vicadel/3D-TFG-VICADEL/STLs/Rotation-Wrist/RotaWrist2V3.stl

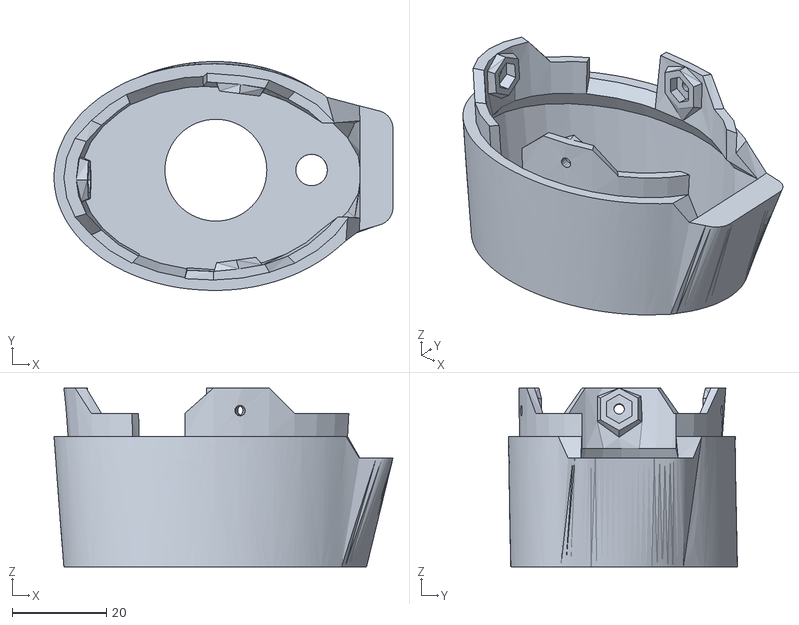
[picture p15: CAD file, 2024-09-07]
STLs/Rotation-Wrist/RotaWrist2V3.stl
71.9 x 48.6 x 38.0
