vicadel/3D-TFG-VICADEL/STLs/Forearm-servo-bed/RobServoBedV6.stl

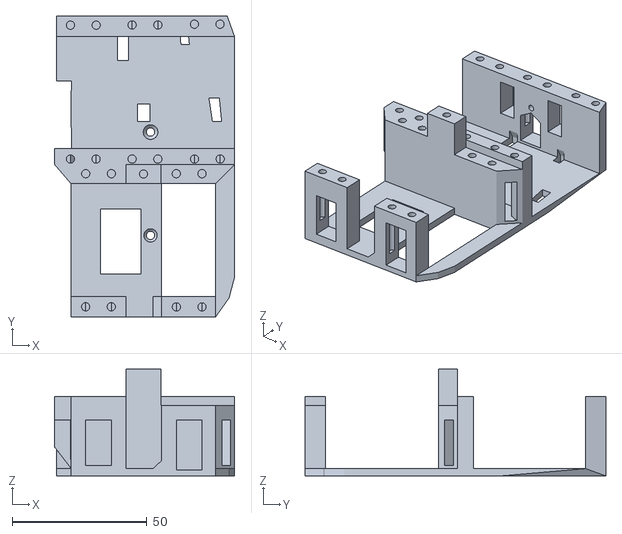
[picture p16: CAD file, 2024-09-07]
STLs/Forearm-servo-bed/RobServoBedV6.stl
66.7 x 111.6 x 39.7
