vicadel/3D-TFG-VICADEL/STLs/Right-Hand/coverfinger1.stl

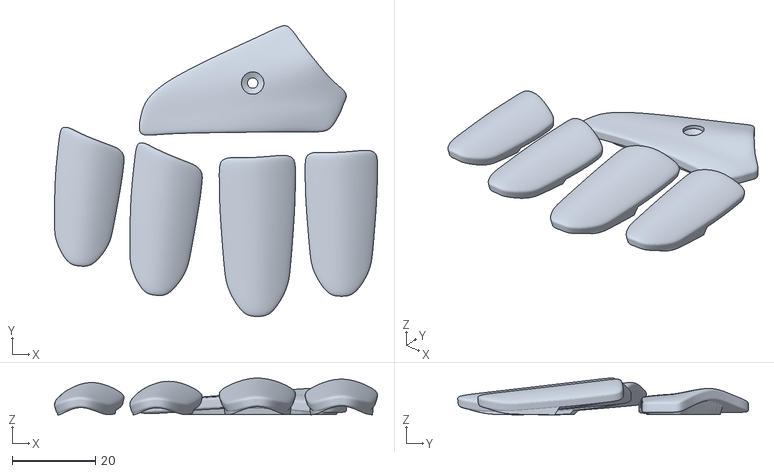
[picture p17: CAD file, 2024-09-07]
STLs/Right-Hand/coverfinger1.stl
77.7 x 69.9 x 8.87
