vicadel/3D-TFG-VICADEL/STLs/Rotation-Wrist/RotaWrist3V3.stl

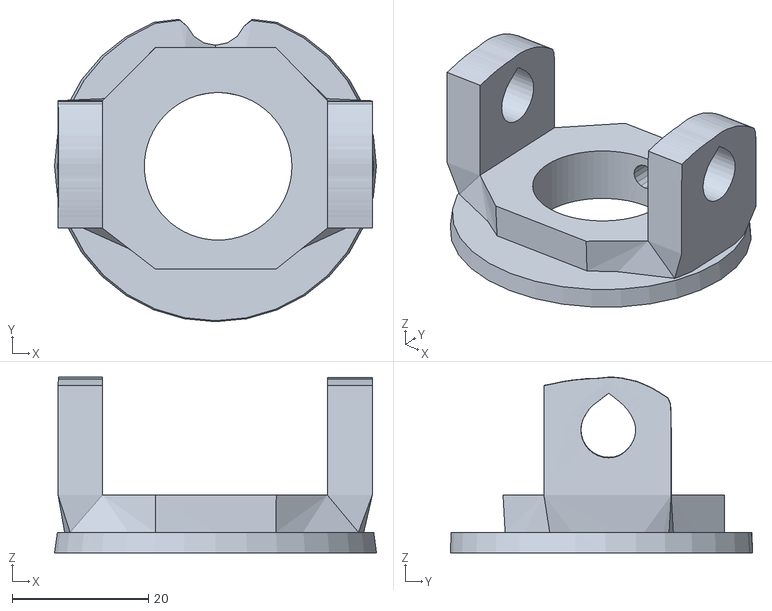
[picture p18: CAD file, 2024-09-07]
STLs/Rotation-Wrist/RotaWrist3V3.stl
47.2 x 44.3 x 25.7
