vicadel/3D-TFG-VICADEL/STLs/Forearm-servo-bed/servo-pulleyX5.stl

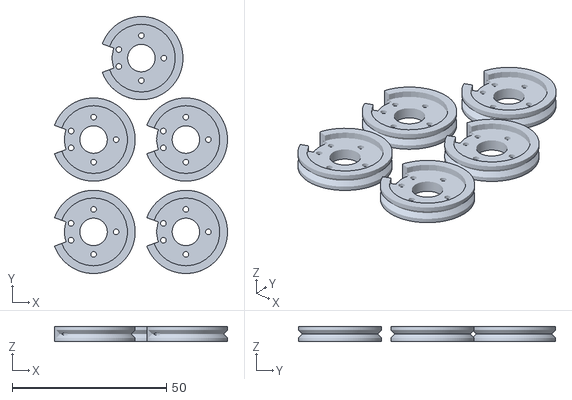
[picture p19: CAD file, 2024-09-07]
STLs/Forearm-servo-bed/servo-pulleyX5.stl
56.1 x 83.4 x 5.00
