vicadel/3D-TFG-VICADEL/STLs/Right-Hand/Index3.stl

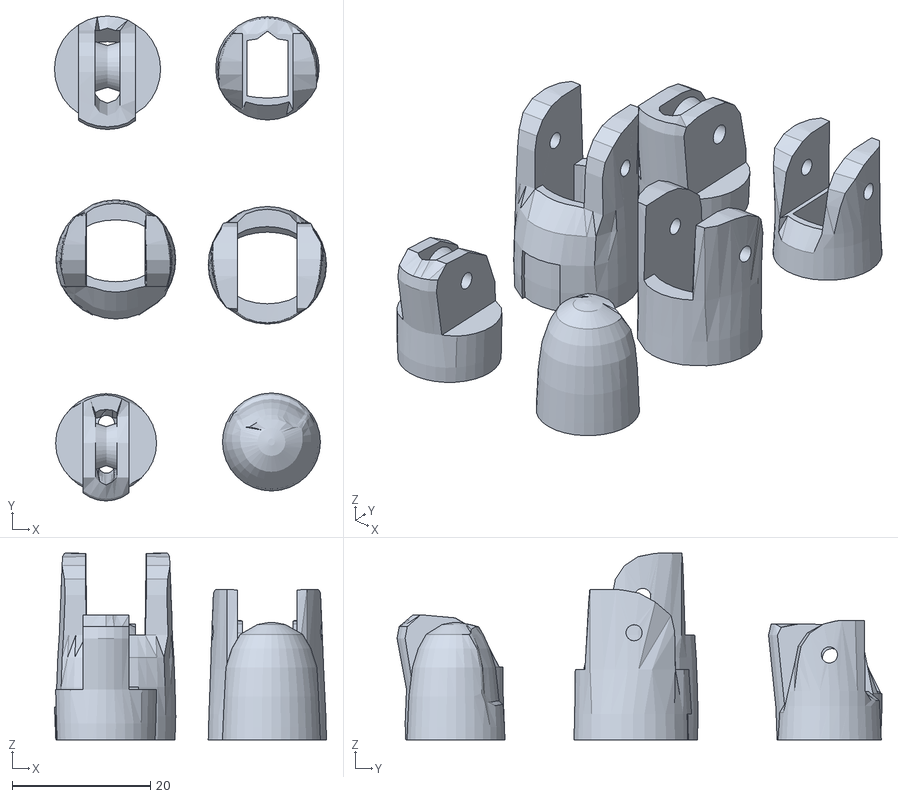
[picture p20: CAD file, 2024-09-07]
STLs/Right-Hand/Index3.stl
39.4 x 70.2 x 27.0
