vicadel/3D-TFG-VICADEL/STLs/Rotation-Wrist/RotaWrist1V4.stl

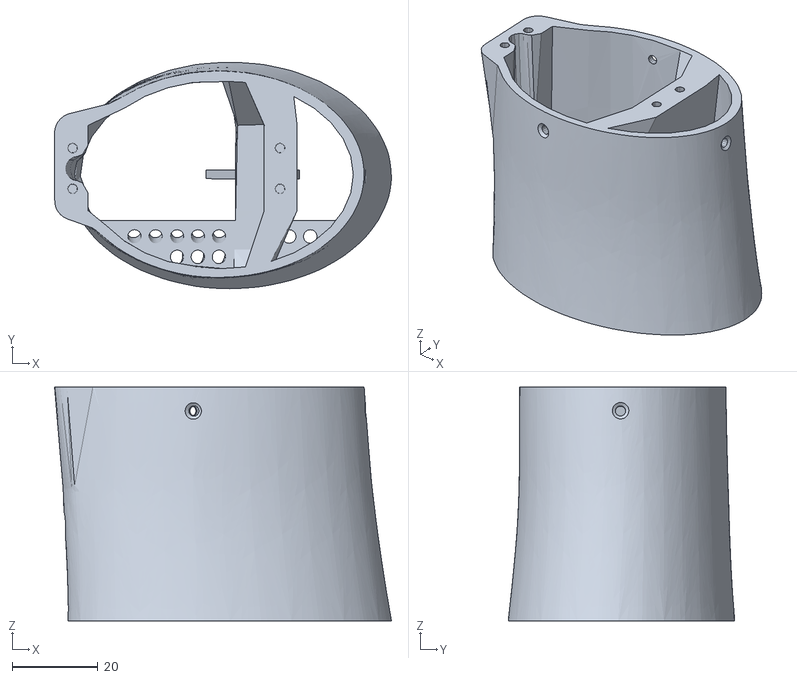
[picture p21: CAD file, 2024-09-07]
STLs/Rotation-Wrist/RotaWrist1V4.stl
78.6 x 52.8 x 54.5
