vicadel/3D-TFG-VICADEL/STLs/Forearm-servo-bed/TensionerRightV1.stl

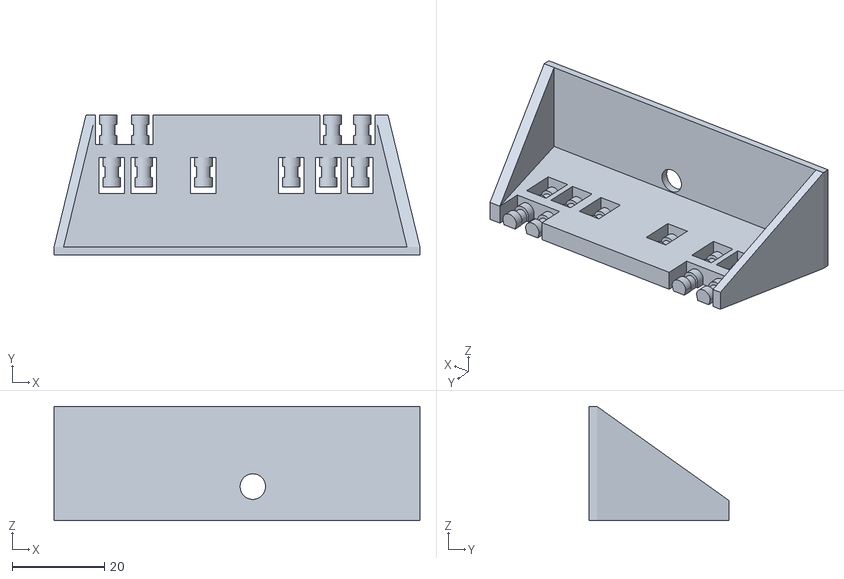
[picture p22: CAD file, 2024-09-07]
STLs/Forearm-servo-bed/TensionerRightV1.stl
79.3 x 30.3 x 24.7
