vicadel/3D-TFG-VICADEL/STLs/Right-Hand/robpart3V4.stl

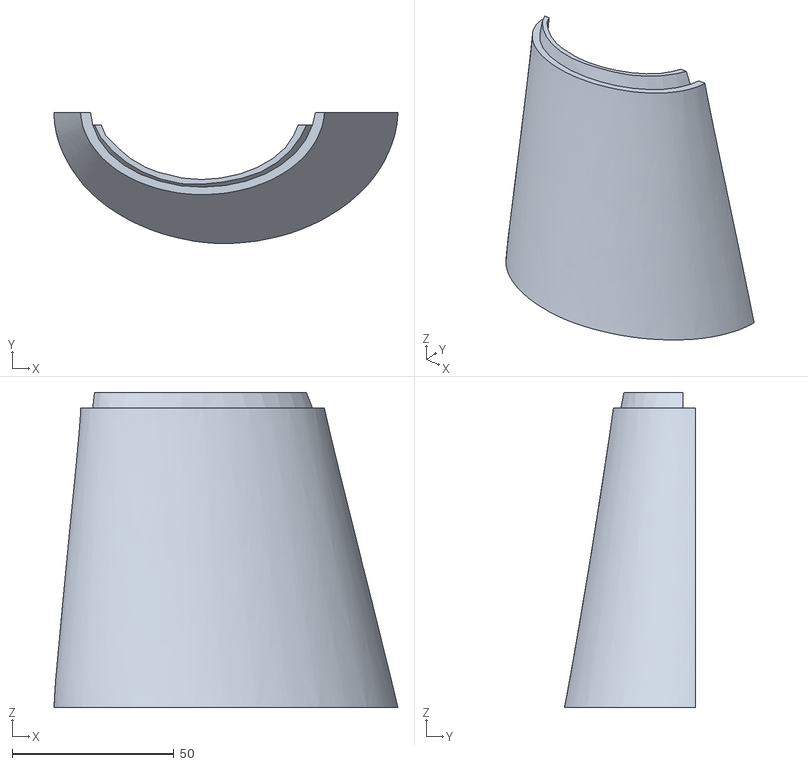
[picture p23: CAD file, 2024-09-07]
STLs/Right-Hand/robpart3V4.stl
106.4 x 40.6 x 97.5
