vicadel/3D-TFG-VICADEL/STLs/Right-Hand/topsurfaceUP6.stl

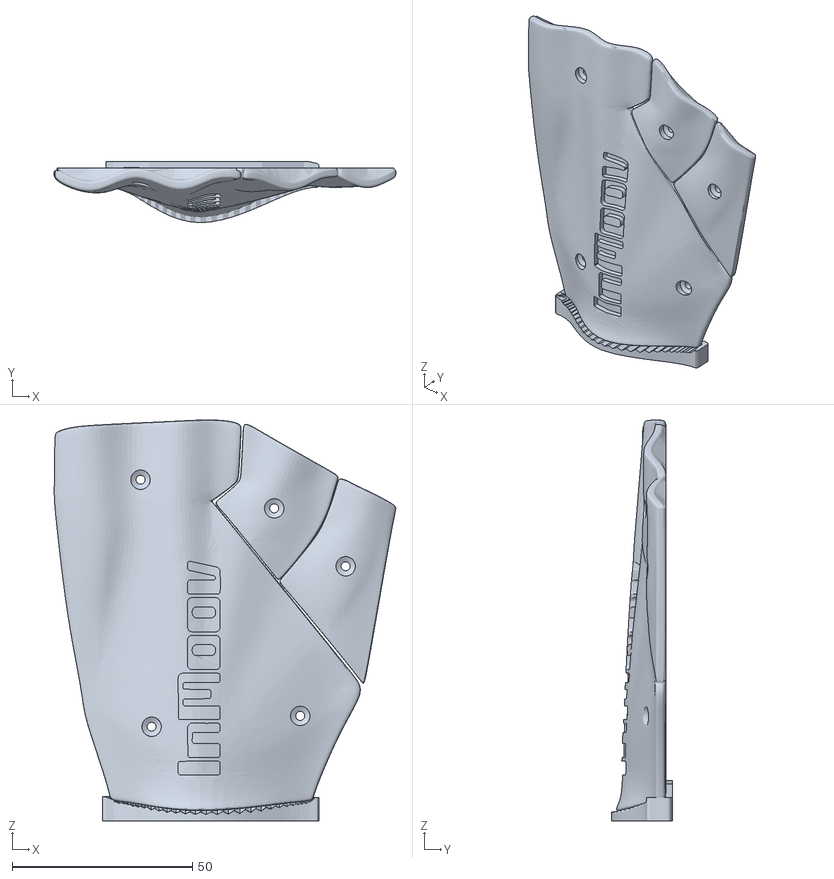
[picture p24: CAD file, 2024-09-07]
STLs/Right-Hand/topsurfaceUP6.stl
94.7 x 17.0 x 111.2
