vicadel/3D-TFG-VICADEL/STLs/Right-Hand/robpart5V4.stl

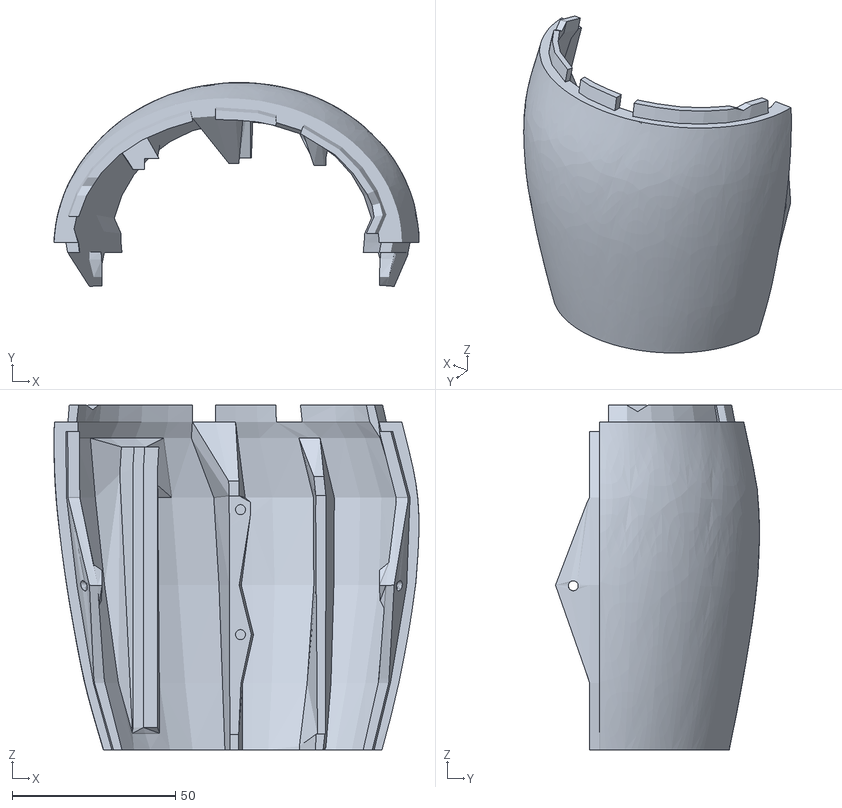
[picture p25: CAD file, 2024-09-07]
STLs/Right-Hand/robpart5V4.stl
111.8 x 62.5 x 105.6
