vicadel/3D-TFG-VICADEL/STLs/Right-Hand/Auriculaire3.stl

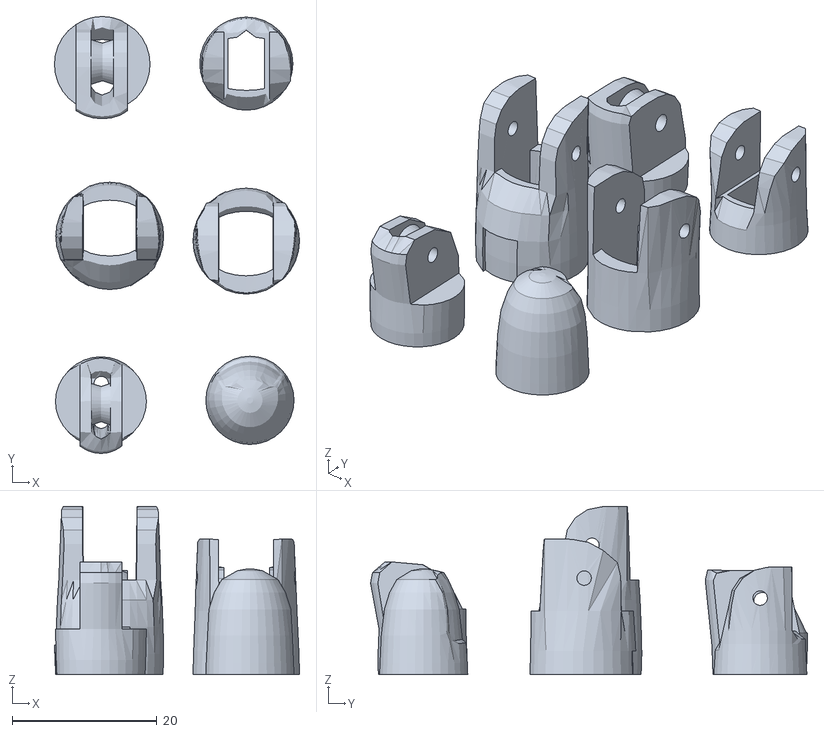
[picture p26: CAD file, 2024-09-07]
STLs/Right-Hand/Auriculaire3.stl
33.8 x 60.3 x 23.2
