vicadel/3D-TFG-VICADEL/STLs/Right-Hand/Majeure3.stl

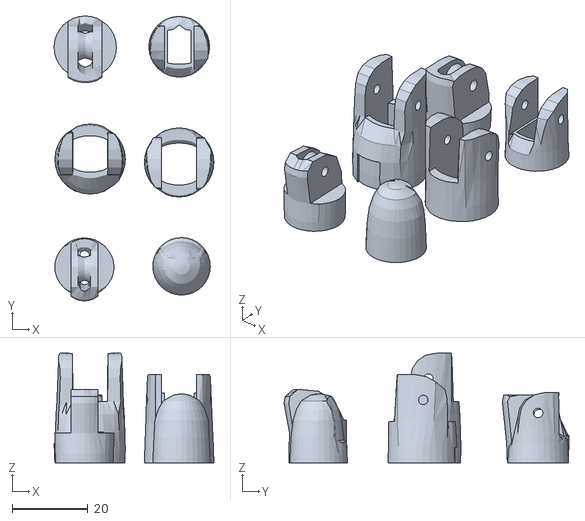
[picture p27: CAD file, 2024-09-07]
STLs/Right-Hand/Majeure3.stl
42.2 x 75.2 x 29.0
