vicadel/3D-TFG-VICADEL/STLs/Right-Hand/robpart2V4.stl

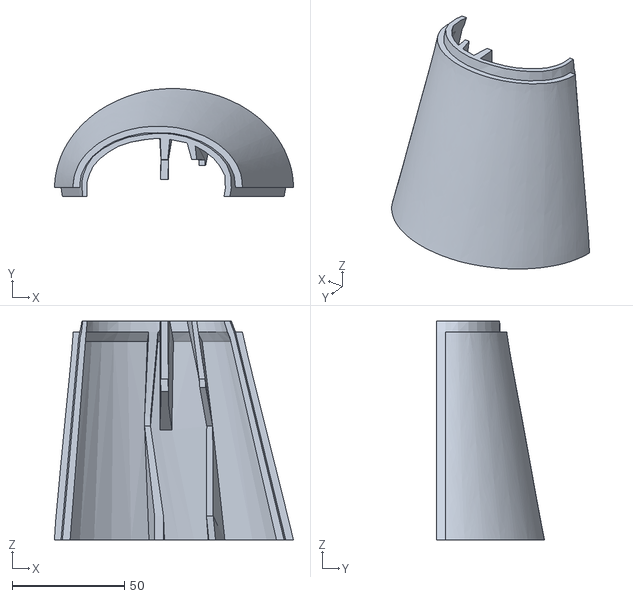
[picture p28: CAD file, 2024-09-07]
STLs/Right-Hand/robpart2V4.stl
106.4 x 48.1 x 97.5
