vicadel/3D-TFG-VICADEL/STLs/Right-Hand/WristsmallV4.stl

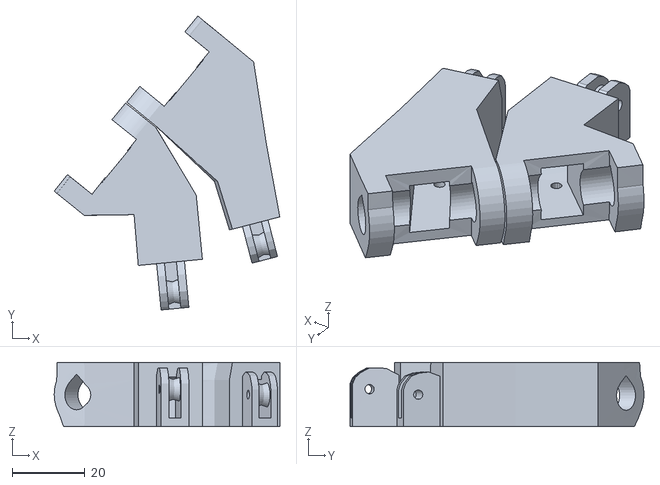
[picture p29: CAD file, 2024-09-07]
STLs/Right-Hand/WristsmallV4.stl
62.0 x 80.8 x 17.7
