vicadel/3D-TFG-VICADEL/STLs/Right-Hand/ESP32support.stl

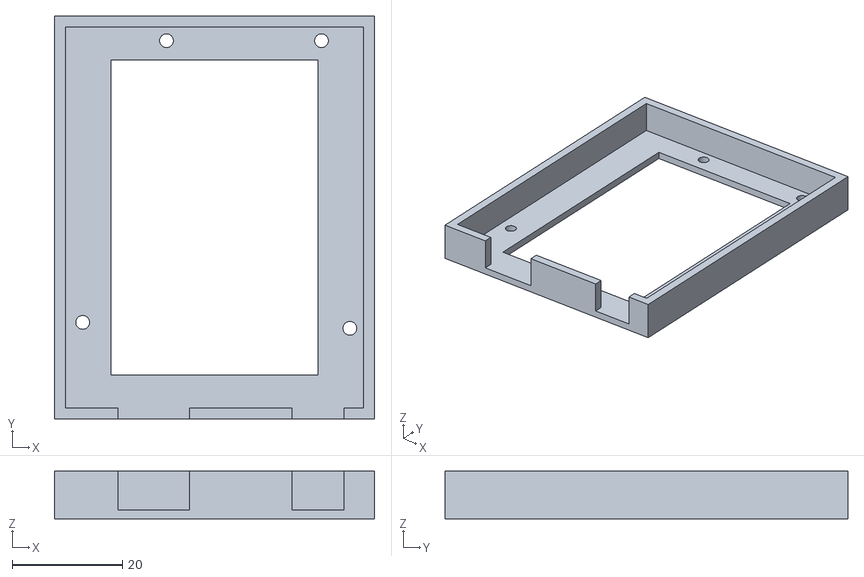
[picture p30: CAD file, 2024-09-07]
STLs/Right-Hand/ESP32support.stl
58.0 x 73.0 x 8.62
