vicadel/3D-TFG-VICADEL/STLs/Right-Hand/topsurface6.stl

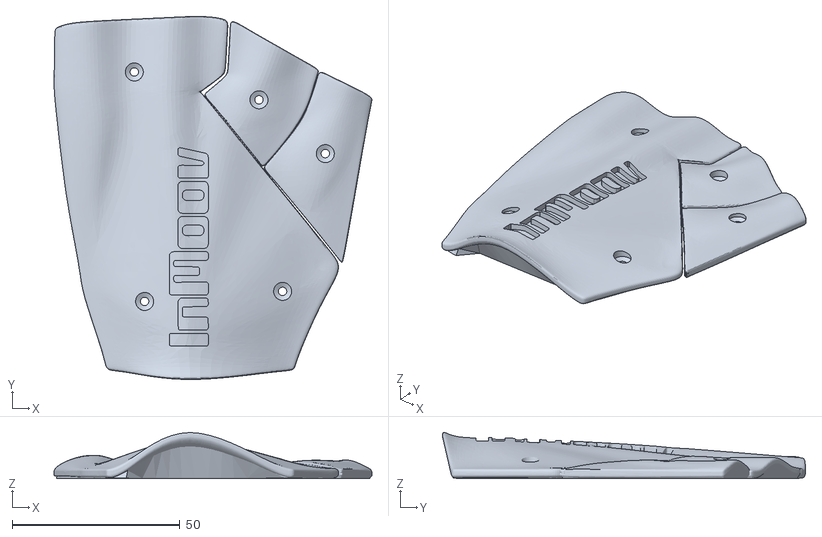
[picture p31: CAD file, 2024-09-07]
STLs/Right-Hand/topsurface6.stl
94.8 x 108.3 x 13.7
