vicadel/3D-TFG-VICADEL/STLs/Right-Hand/thumb5.stl

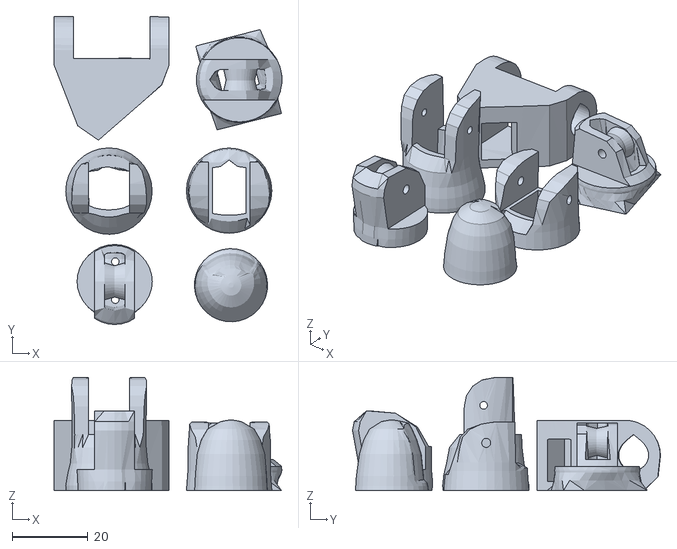
[picture p32: CAD file, 2024-09-07]
STLs/Right-Hand/thumb5.stl
60.1 x 81.2 x 29.8
