vicadel/3D-TFG-VICADEL/STLs/Right-Hand/FINAL-TOPSURFACE.stl

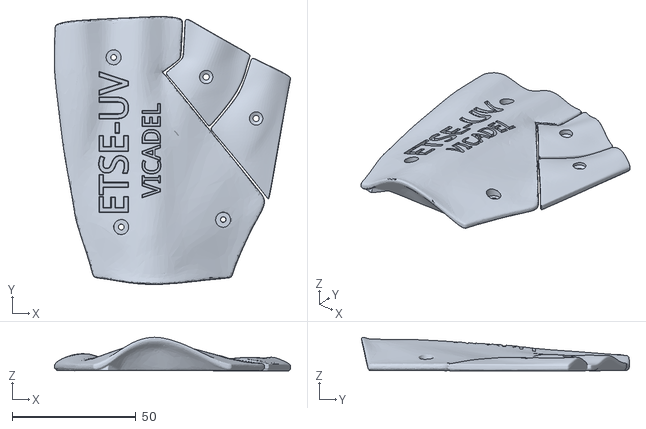
[picture p33: CAD file, 2024-09-07]
STLs/Right-Hand/FINAL-TOPSURFACE.stl
95.3 x 108.2 x 13.5
